Nilon123456789/Drone/Arduino/Test_Scripts/ESC_Test/ESC_Test.ino

#include <Servo.h>


//                                                               (2)   (1)
//ESC                                                            CW    CCW
#define EscPinFR 11 //CCW  (1)                                     ╲  ╱
#define EscPinFL 10 //CW (2)                                        ▉     ↑ forward
#define EscPinBR 9 //CW  (3)                                      ╱  ╲
#define EscPinBL 6 //CCW   (4)                                   CCW    CW
//                                                              (4)    (3)

//Remote
#define ThrotlePin A0

/******ESC Values******/
const int escIdle = 1000; //ESC idle speed
const int escMin = 1100; //ESC min working speed (for all esc)
const int escMax = 2000; //ESC max working spees (for all esc)

/******RC Values******/
const int throttleMin=995, throttleMax=1988;

Servo ESC_FL, ESC_FR, ESC_BL, ESC_BR;

bool isReady = false;

void setup() {
  // put your setup code here, to run once:
  Serial.begin(115200);

  Serial.println("Seting up ESCs");
  
  //Set the pin for each ESC
  ESC_FL.attach(EscPinFR);
  ESC_FR.attach(EscPinFL);
  ESC_BL.attach(EscPinBL);
  ESC_BR.attach(EscPinBR);
  Serial.print('>');

  
  //Set the ESC to max speed
  ESC_FL.writeMicroseconds(escMax); 
  ESC_FR.writeMicroseconds(escMax);
  ESC_BL.writeMicroseconds(escMax); 
  ESC_BR.writeMicroseconds(escMax);

  tone(3, 3000, 750);
  delay(5000);
  tone(3, 3000, 750);
  Serial.print('>');

  //Set the ESC to the min speed
  ESC_FL.writeMicroseconds(escIdle); 
  ESC_FR.writeMicroseconds(escIdle);
  ESC_BL.writeMicroseconds(escIdle); 
  ESC_BR.writeMicroseconds(escIdle);

  delay(5000);
  tone(3, 3000, 750);

  Serial.println("Seting up Reciver");

  pinMode(ThrotlePin, INPUT);


  isReady = true;
  Serial.println("Ready");
}

void loop() {
  if(!isReady) return;//Wait for ready

  int _throttle = map(pulseIn(ThrotlePin,HIGH),throttleMin,throttleMax,escIdle,escMax);
  Serial.println(_throttle);
  //Write the ESC values
  ESC_FL.writeMicroseconds(_throttle);
  ESC_FR.writeMicroseconds(_throttle);
  ESC_BL.writeMicroseconds(_throttle);
  ESC_BR.writeMicroseconds(_throttle);
}
